pavanegasg/Sistemas-Embebidos/Documentación/Sensores/HX711 y celda de carga/readme.md

## ¿Que es HX711?

El modulo HX711 es un dispositivo que actúa como conversor analógico a digital de 24 bits de precisión diseñado para trabajar con sensores tipo puente como las celdas de carga para medición de peso. Este está compuesto básicamente por un multiplexor, un PGA (amplificador de ganancia programable), un conversor analógico digital y una interfaz digital que permite la conexión digital con el Arduino.

## ¿Que es una celda de carga?

Una celda de carga es un puente de Wheastone el cual emplea resistencias que varían su valor en función de la deformación mecánica que sufre la celda cuando esta es sometida a una fuerza, en este caso el peso de un objeto. 

## Prerrequisitos

Para la utilización de este sensor se empleo de la libreria _HX_711_ la cual se puede descargar en el IDE de Arduino.

## Calibración

Para la calibración de este se empleo un programa en el cual se ingresa el peso en gramos del objeto que se posiciona en la celda de carga, en el caso de la celda de carga numero 1 se encontró que el valor de calibración es -391.55.

<p align="center">
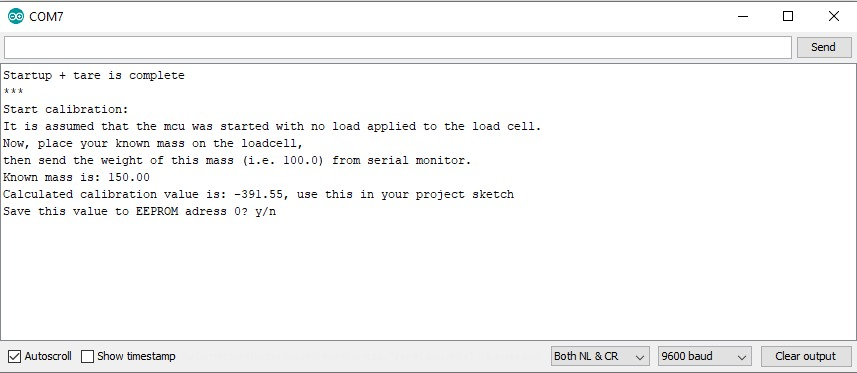
[picture p14: Documentación/Sensores/HX711 y celda de carga/CeldaCalibracion.jpeg]
  
</p>

## Prueba de la calibración

El valor de calibración obtenido en el punto anterior se ingresa al programa _Read_1x_load_cell_, con este arroja el peso del objeto que se encuentre en la celda de carga, a continuación de presente lo obtenido al cambiar una pesa de 150 g a una pesa de 213 g.

<p align="center">
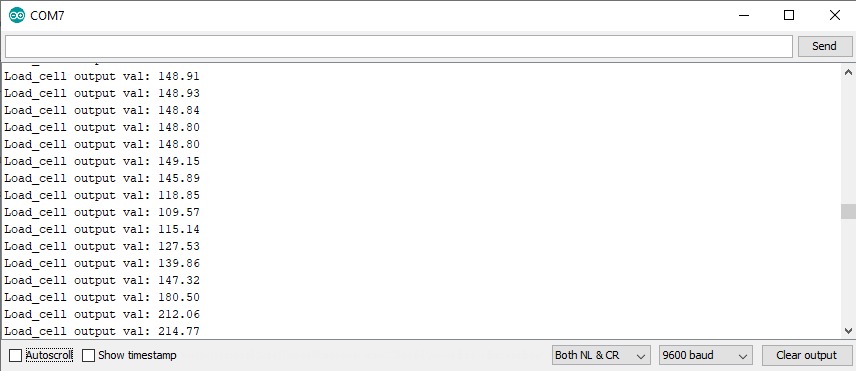
[picture p15: Documentación/Sensores/HX711 y celda de carga/CeldaCalibrada.jpeg]
  
</p>
