pavanegasg/Sistemas-Embebidos/Documentos/Test de los 6 sombreros/sombrerosGabriel.png

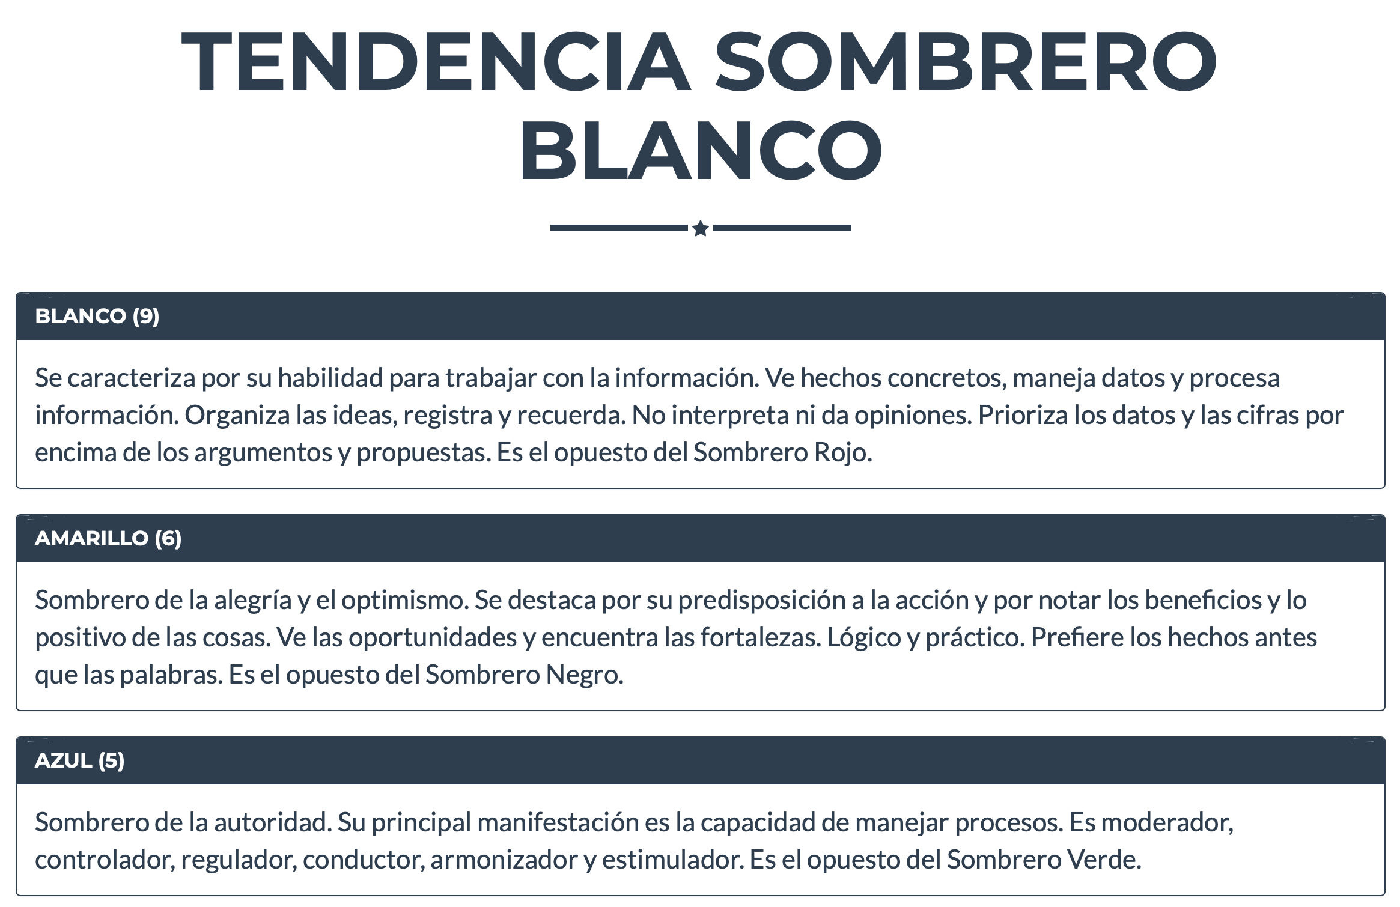
Documentos/Test de los 6 sombreros/sombrerosGabriel.png
