pavanegasg/Sistemas-Embebidos/Documentos/Test de los 6 sombreros/sombrerosNicold.png

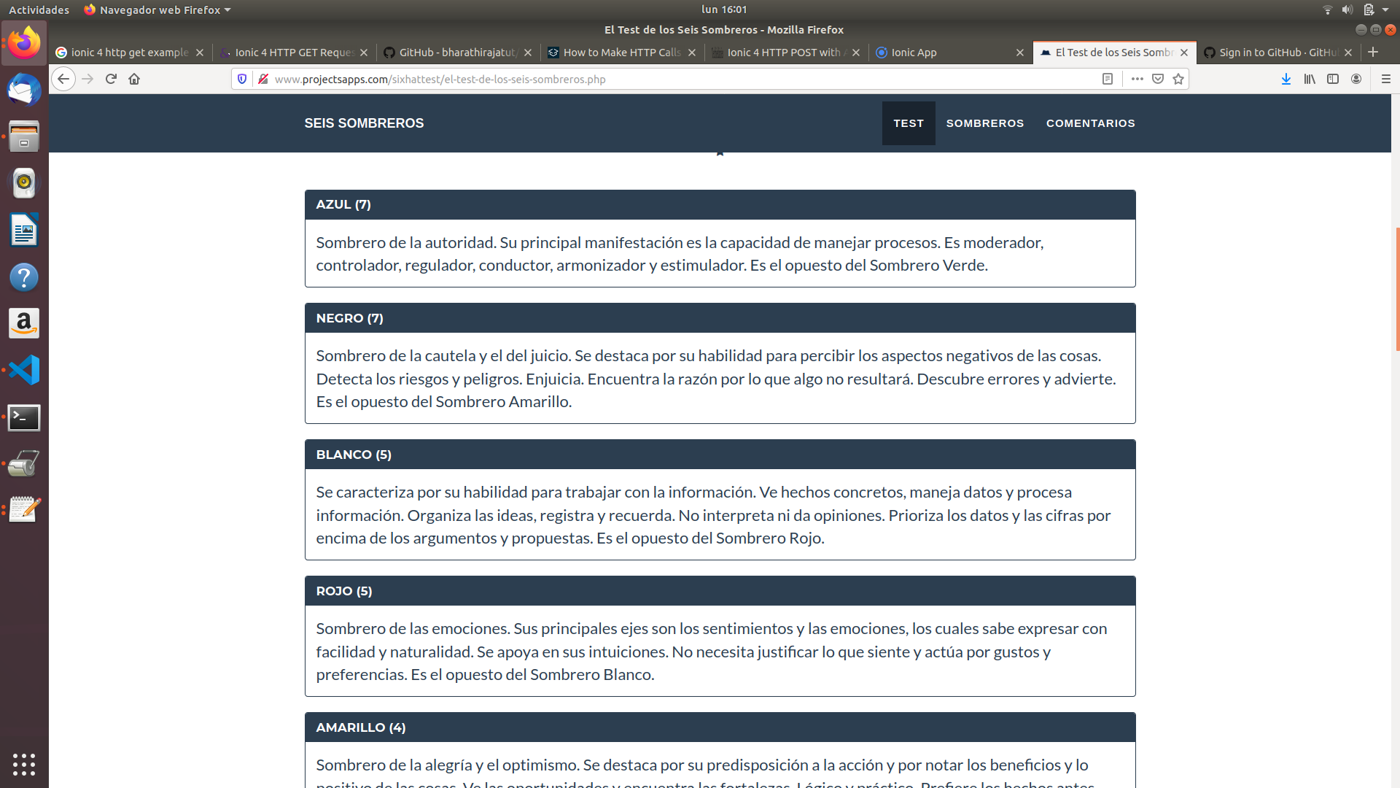
Documentos/Test de los 6 sombreros/sombrerosNicold.png
